AGS-ERASMUS26-RFID-Games/Mastermind/mastermind_kicad/mastermind.kicad_sch

## KiCad design mastermind_kicad/mastermind.kicad_sch (2026-09-26)

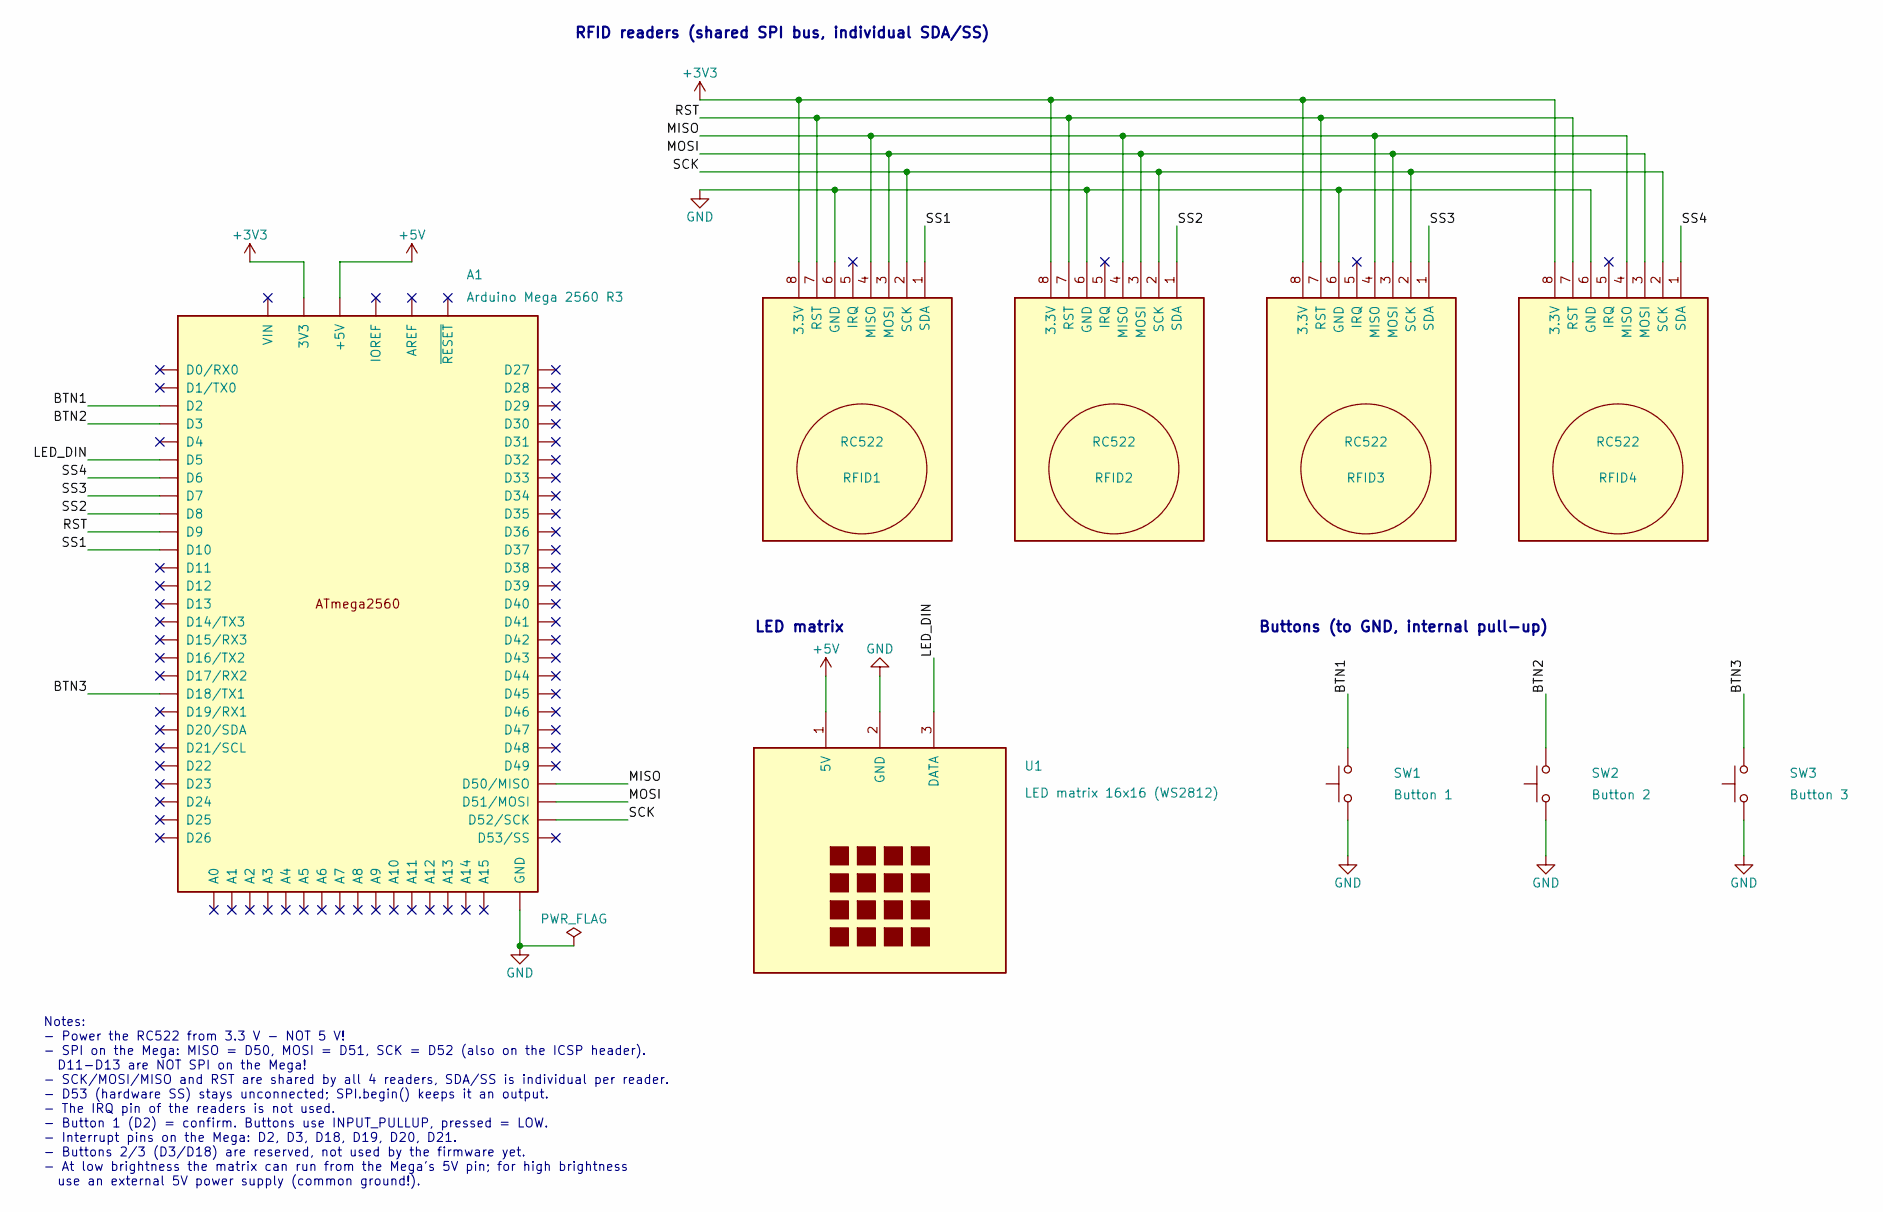
[picture p8: schematic mastermind.kicad_sch]

Parts:
A1: Arduino Mega 2560 R3
RFID1, RFID2, RFID3, RFID4: RC522
SW1: Button 1
SW2: Button 2
SW3: Button 3
U1: LED matrix 16x16 (WS2812)

Connections:
+3V3: A1.3V3, RFID1.8 (3.3V), RFID2.8 (3.3V), RFID3.8 (3.3V), RFID4.8 (3.3V)
+5V: A1.5V (+5V), U1.1 (5V)
BTN1: A1.D2, SW1.2
BTN2: A1.D3, SW2.2
BTN3: A1.D18 (D18/TX1), SW3.2
GND: A1.GND, RFID1.6 (GND), RFID2.6 (GND), RFID3.6 (GND), RFID4.6 (GND), SW1.1, SW2.1, SW3.1, U1.2 (GND)
LED_DIN: A1.D5, U1.3 (DATA)
MISO: A1.D50 (D50/MISO), RFID1.4 (MISO), RFID2.4 (MISO), RFID3.4 (MISO), RFID4.4 (MISO)
MOSI: A1.D51 (D51/MOSI), RFID1.3 (MOSI), RFID2.3 (MOSI), RFID3.3 (MOSI), RFID4.3 (MOSI)
RST: A1.D9, RFID1.7 (RST), RFID2.7 (RST), RFID3.7 (RST), RFID4.7 (RST)
SCK: A1.D52 (D52/SCK), RFID1.2 (SCK), RFID2.2 (SCK), RFID3.2 (SCK), RFID4.2 (SCK)
SS1: A1.D10, RFID1.1 (SDA)
SS2: A1.D8, RFID2.1 (SDA)
SS3: A1.D7, RFID3.1 (SDA)
SS4: A1.D6, RFID4.1 (SDA)

Notes on the sheet:
RFID readers (shared SPI bus, individual SDA/SS)
LED matrix
Buttons (to GND, internal pull-up)
Notes: - Power the RC522 from 3.3 V - NOT 5 V! - SPI on the Mega: MISO = D50, MOSI = D51, SCK = D52 (also on the ICSP header). D11-D13 are NOT SPI on the Mega! - SCK/MOSI/MISO and RST are shared by all 4 readers, SDA/SS is individual per reader. - D53 (hardware SS) stays unconnected; SPI.begin() ke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
